kolszewska16/stm32h7-acoustic-speed-camera/AcousticSpeedCamera/Core/Inc/hardware.h

#ifndef INC_HARDWARE_H_
#define INC_HARDWARE_H_

#include "stm32h7xx_hal.h"
#include "stm32h7xx_nucleo.h"

extern COM_InitTypeDef BspCOMInit;
extern DFSDM_Filter_HandleTypeDef hdfsdm1_filter0;
extern DFSDM_Filter_HandleTypeDef hdfsdm1_filter1;

#endif /* INC_HARDWARE_H_ */
