kolszewska16/stm32h7-acoustic-speed-camera/AcousticSpeedCamera/Core/Inc/os_objects.h

#ifndef INC_OS_OBJECTS_H_
#define INC_OS_OBJECTS_H_

#include <stdbool.h>
#include "FreeRTOS.h"
#include "cmsis_os2.h"
#include "semphr.h"

extern volatile bool camera_ready;
extern volatile bool sd_ready;
extern volatile bool ui_ready;

extern osMutexId_t uartMutex;
extern osMutexAttr_t uartMutex_attr;

extern osThreadId_t audioTaskHandle;
extern osThreadId_t displayTaskHandle;
extern osThreadId_t cameraTaskHandle;

extern const osThreadAttr_t audioTask_attr;
extern const osThreadAttr_t displayTask_attr;
extern const osThreadAttr_t cameraTask_attr;

#endif /* INC_OS_OBJECTS_H_ */
