kolszewska16/stm32h7-acoustic-speed-camera/AcousticSpeedCamera/Core/Src/audio_task.c

#include "audio_task.h"
#include "FreeRTOS.h"
#include "task.h"
#include "os_objects.h"
#include "audio_processor.h"
#include "logger.h"
#include "ui.h"

#define NOISE_THRESHOLD 40.0f
#define HOLD_OFF_TIME_MS 2000

void vAudioTask(void *parameter) {
	LOG_INFO("audio task start");

	while(!camera_ready || !ui_ready) {
		osDelay(50);
	}

	static float32_t dBA_max = -1000.0f;
	uint32_t last_trigger_time = 0;

	audio_dsp_init();
	if(audio_hardware_start() != HAL_OK) {
		LOG_ERROR("DFSDM: initialization failed");
		vTaskDelete(NULL);
		return;
	}

	LOG_INFO("audio initialization completed");

	while(1) {
		uint32_t flags = osThreadFlagsWait(0x03, osFlagsWaitAny, osWaitForever);
		uint32_t part_idx = -1;
		if(flags & 0x01) {
			part_idx = 0;
		}
		else if(flags & 0x02) {
			part_idx = 1;
		}

		uint32_t offset = part_idx * SAMPLES;
		float32_t dBA_avg = process_audio_frame(dmabuff_L, dmabuff_R, offset);

		uint32_t now = xTaskGetTickCount();
		if(dBA_avg > NOISE_THRESHOLD) {
			if((now - last_trigger_time) >= pdMS_TO_TICKS(HOLD_OFF_TIME_MS)) {
				last_trigger_time = now;
				if(cameraTaskHandle != NULL) {
					xTaskNotifyGive((TaskHandle_t)cameraTaskHandle);
				}
			}
		}

		if(dBA_avg > dBA_max) {
			dBA_max = dBA_avg;
		}

		update_ui(dBA_avg, dBA_max);
	}

	vTaskDelete(NULL);
}
